itacarobotics/Metis/assets/gallery/end_effector.png

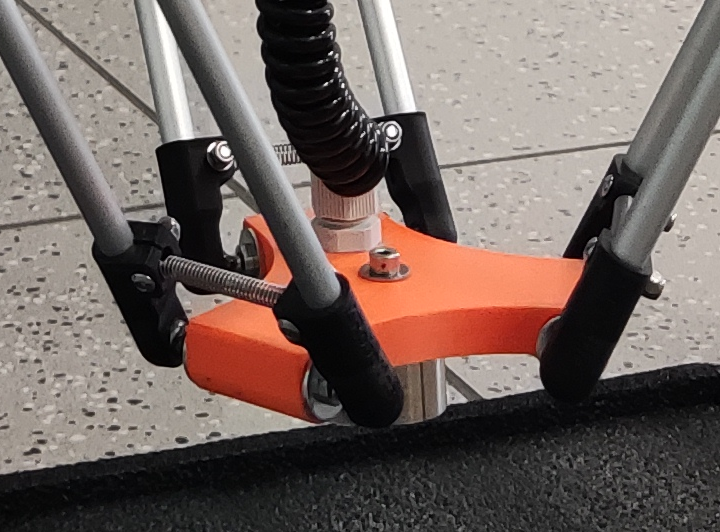
assets/gallery/end_effector.png
