itacarobotics/Metis/docs/assets/images/belt_tensioning.png

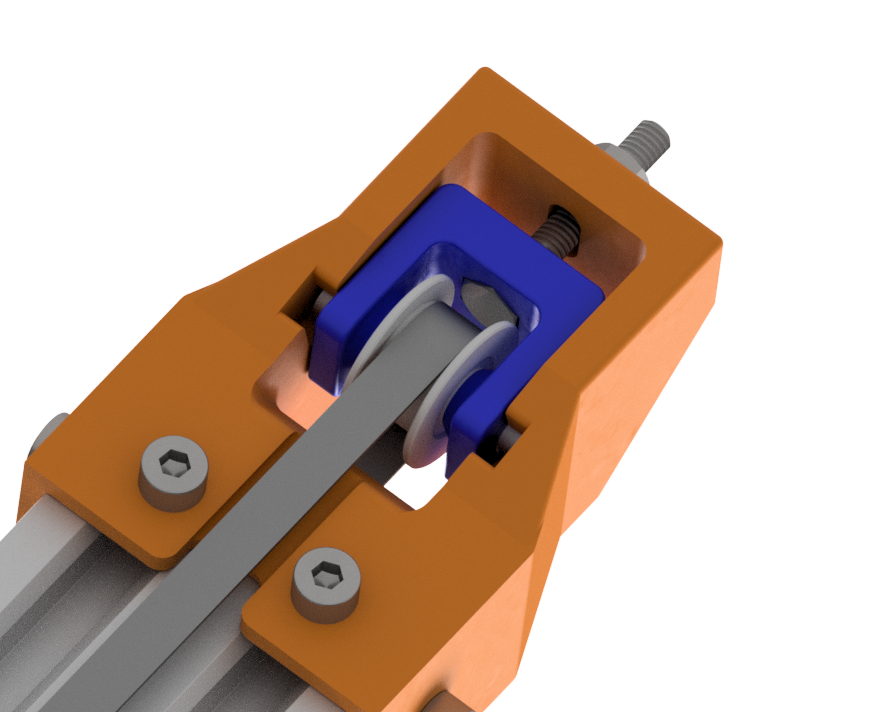
docs/assets/images/belt_tensioning.png
