itacarobotics/Metis/docs/assets/images/topological_optimization.png

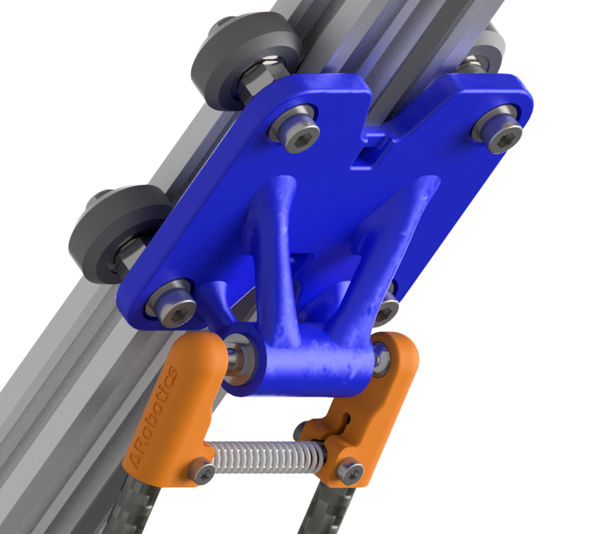
docs/assets/images/topological_optimization.png
