itacarobotics/Metis/docs/assets/plots/gradient_descent.png

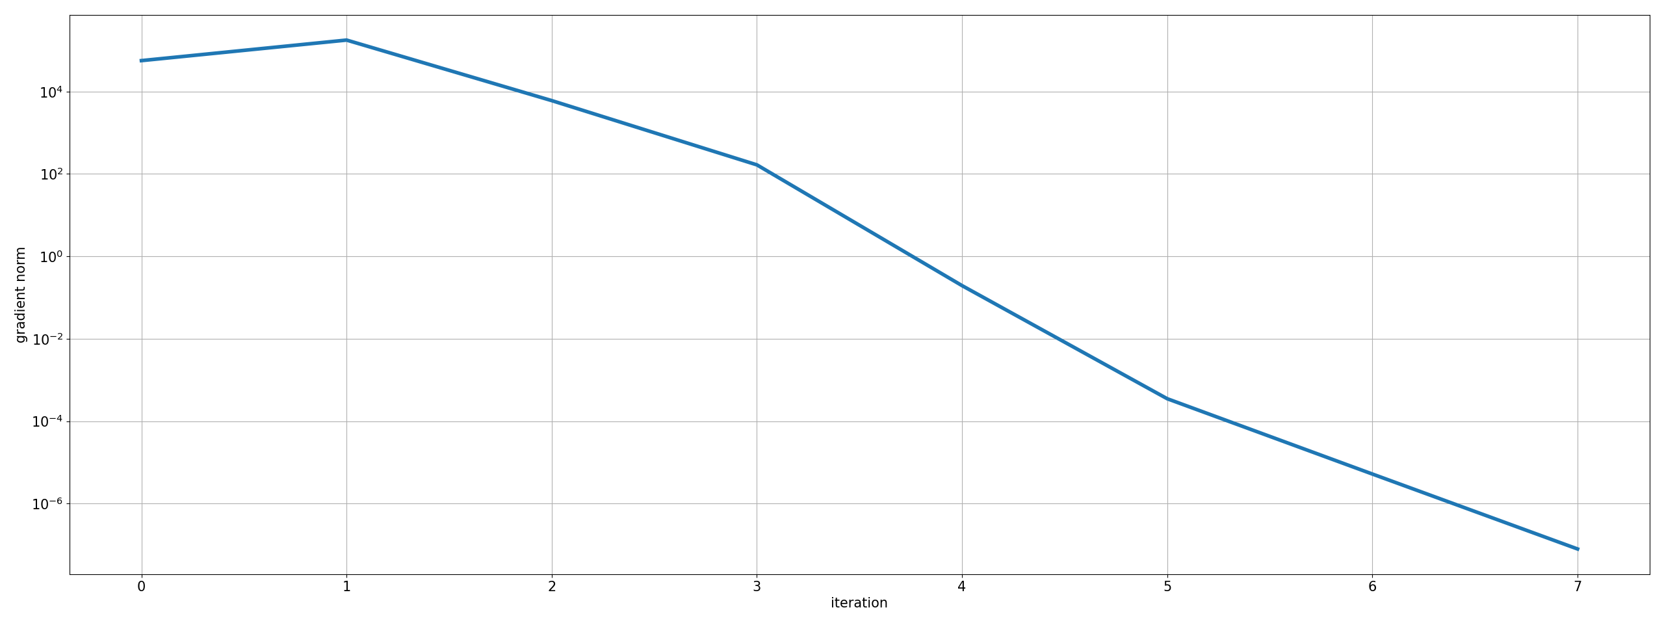
docs/assets/plots/gradient_descent.png
