itacarobotics/Metis/docs/assets/plots/joint_space_path.png

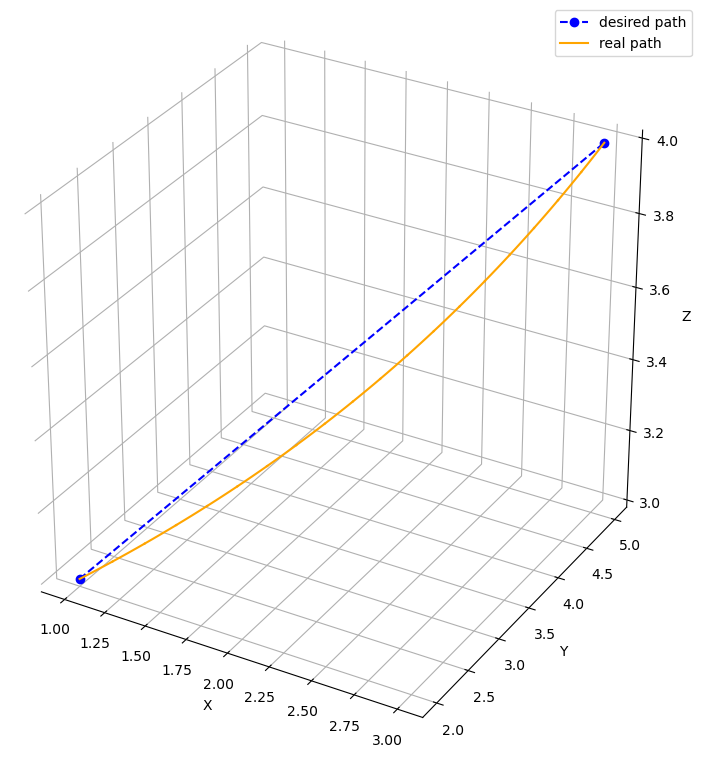
docs/assets/plots/joint_space_path.png
