itacarobotics/Metis/docs/assets/plots/nodes_diagram.png

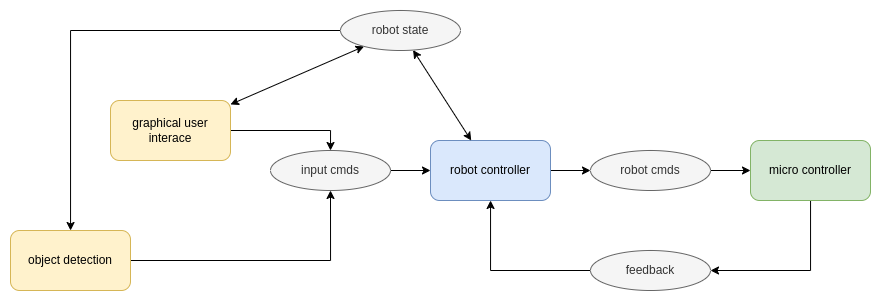
docs/assets/plots/nodes_diagram.png
