itacarobotics/Metis/docs/assets/plots/quintic_polynomial.png

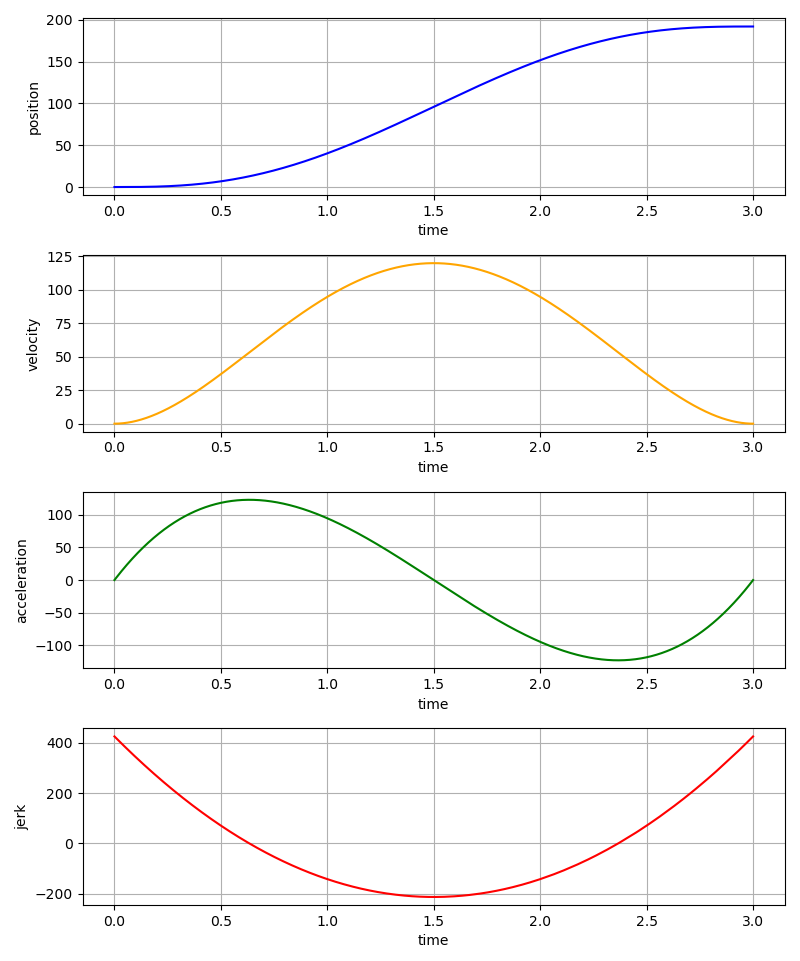
docs/assets/plots/quintic_polynomial.png
