itacarobotics/Metis/docs/assets/plots/task_space_path.png

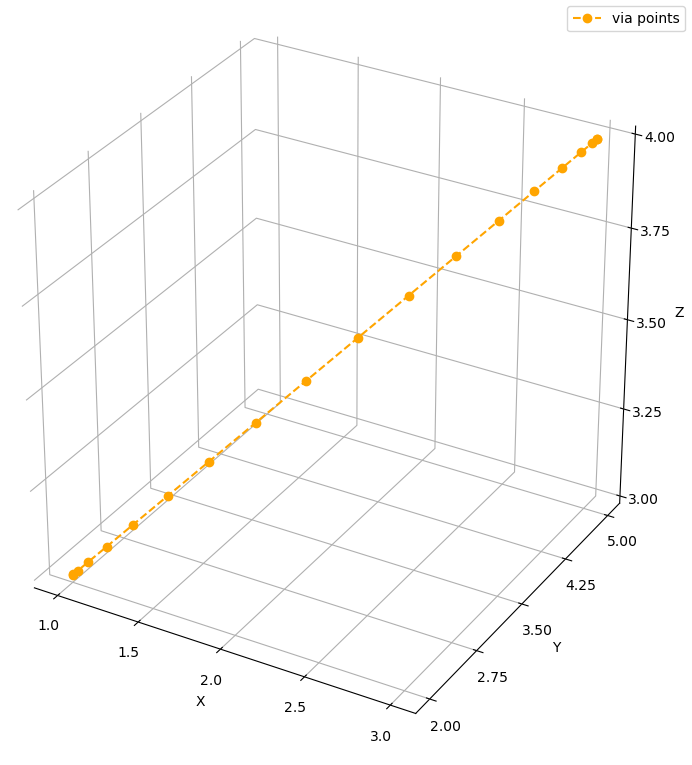
docs/assets/plots/task_space_path.png
