itacarobotics/Metis/src/deltarobot_inputs/test/computer_vision/assets/tests/image6.png

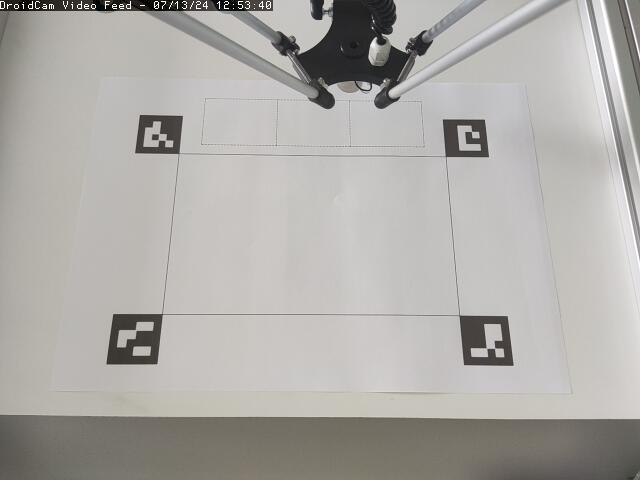
src/deltarobot_inputs/test/computer_vision/assets/tests/image6.png
