itacarobotics/Metis/src/deltarobot_inputs/test/computer_vision/assets/tests/image7.png

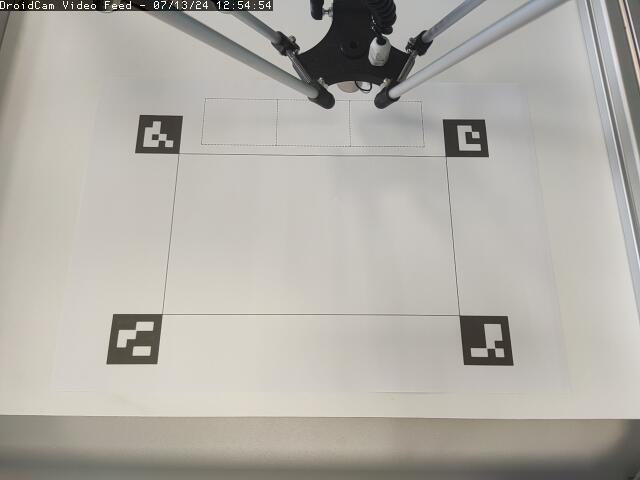
src/deltarobot_inputs/test/computer_vision/assets/tests/image7.png
