itacarobotics/Metis/src/firmware_esp32/src/robot_interfaces.h

#ifndef CUSTOM_MESSAGES_H
#define CUSTOM_MESSAGES_H

#include <micro_custom_messages/msg/joint_trajectory.h>
#include <micro_custom_messages/msg/joint_trajectory_array.h>

#include <std_msgs/msg/bool.h>

#endif  // CUSTOM_MESSAGES_H
